OllieBck/MorsePlay/MorsePlay--App/res/screen/ios/screen-iphone-portrait.png

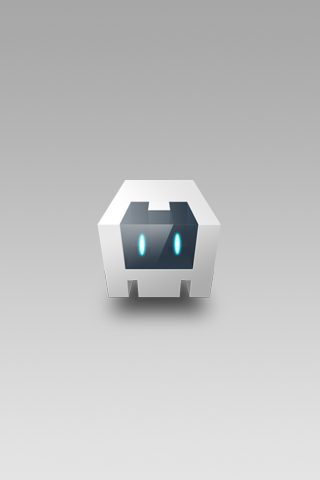
MorsePlay--App/res/screen/ios/screen-iphone-portrait.png
