OllieBck/MorsePlay/MorsePlay--App/res/screen/bada-wac/screen-type4.png

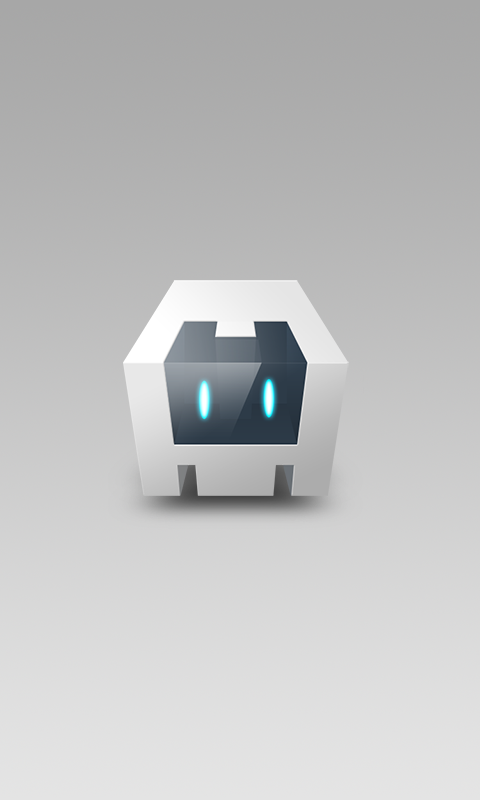
MorsePlay--App/res/screen/bada-wac/screen-type4.png
