OllieBck/MorsePlay/MorsePlay--App/res/screen/android/screen-hdpi-landscape.png

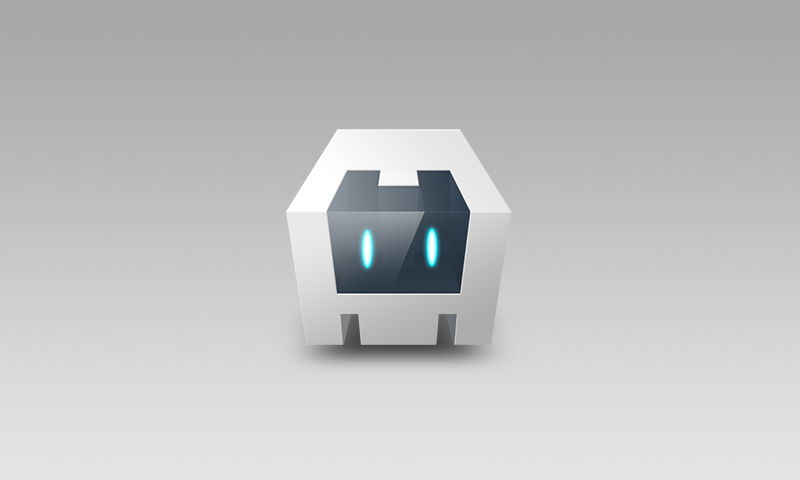
MorsePlay--App/res/screen/android/screen-hdpi-landscape.png
