OllieBck/MorsePlay/MorsePlay--App/res/screen/android/screen-mdpi-landscape.png

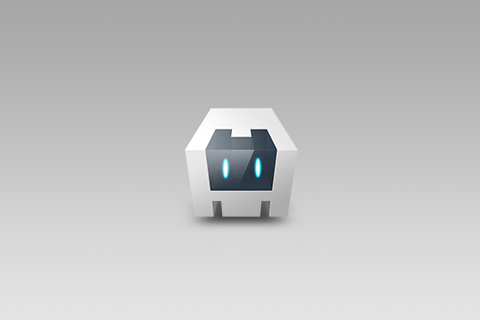
MorsePlay--App/res/screen/android/screen-mdpi-landscape.png
