OllieBck/MorsePlay/MorsePlay--App/res/screen/android/screen-mdpi-portrait.png

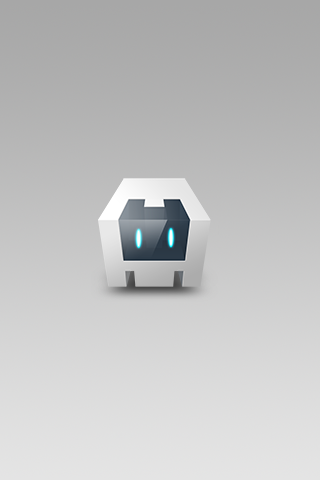
MorsePlay--App/res/screen/android/screen-mdpi-portrait.png
