OllieBck/MorsePlay/MorsePlay--App/res/screen/blackberry/screen-225.png

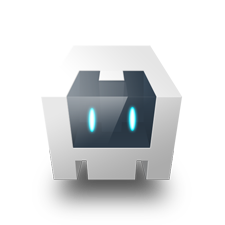
MorsePlay--App/res/screen/blackberry/screen-225.png
