OllieBck/MorsePlay/MorsePlay--App/res/screen/ios/screen-ipad-portrait-2x.png

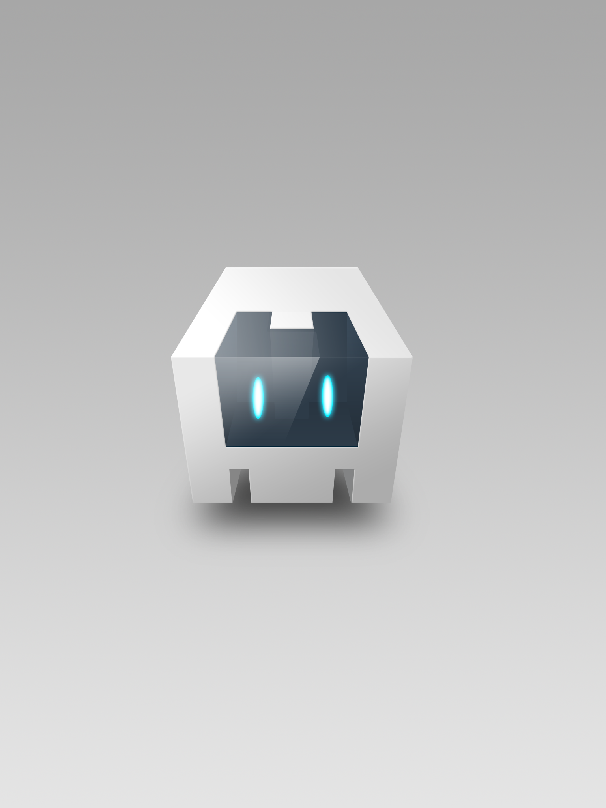
MorsePlay--App/res/screen/ios/screen-ipad-portrait-2x.png
