OllieBck/MorsePlay/MorsePlay--App/res/screen/ios/screen-iphone-portrait-568h-2x.png

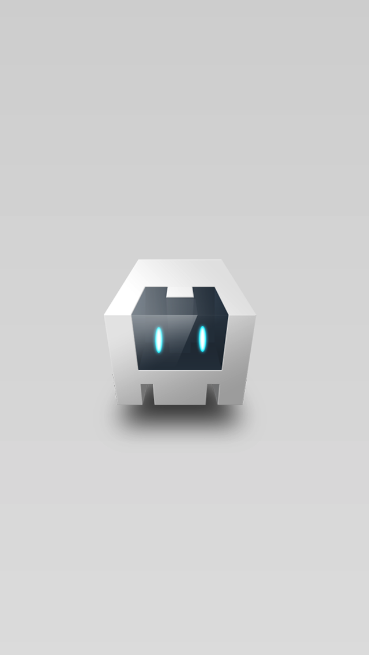
MorsePlay--App/res/screen/ios/screen-iphone-portrait-568h-2x.png
