OllieBck/MorsePlay/MorsePlay--App/res/screen/windows-phone/screen-portrait.jpg

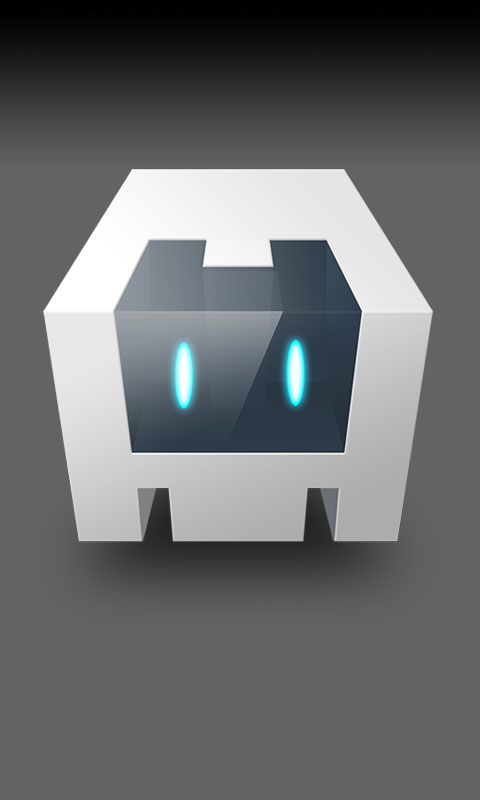
MorsePlay--App/res/screen/windows-phone/screen-portrait.jpg
